krelsaid/Pickup-Winder/picture/Image 2.jpeg

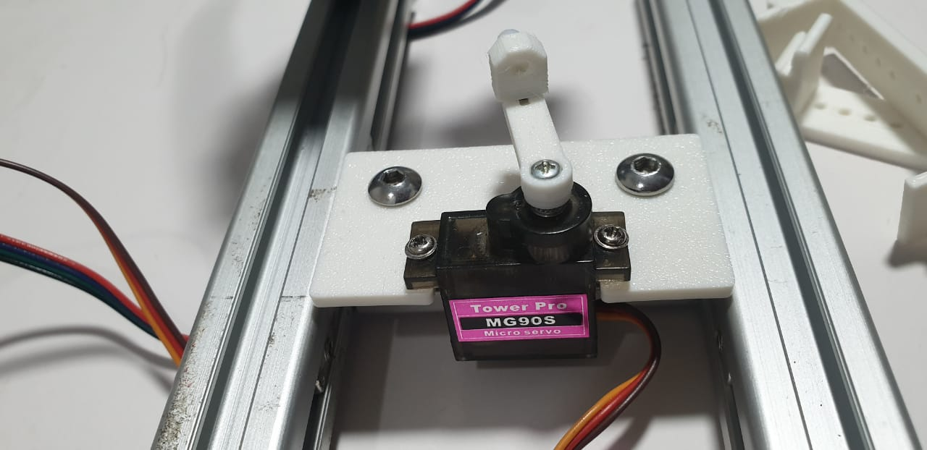
picture/Image 2.jpeg
